dczia/Defcon26-Badge/Images/2018CardFront.jpg

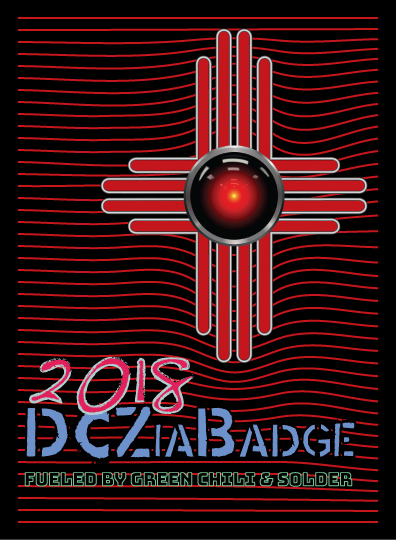
Images/2018CardFront.jpg
