dczia/Defcon26-Badge/Images/DCZia Line Sticker.png

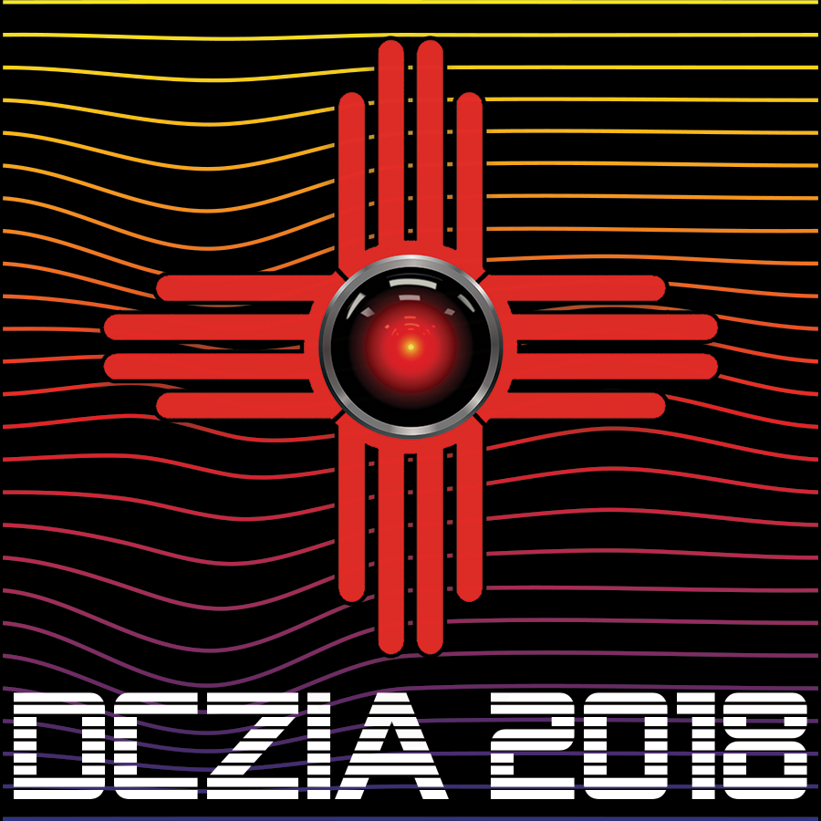
Images/DCZia Line Sticker.png
