dczia/Defcon26-Badge/Images/DCZPolo.png

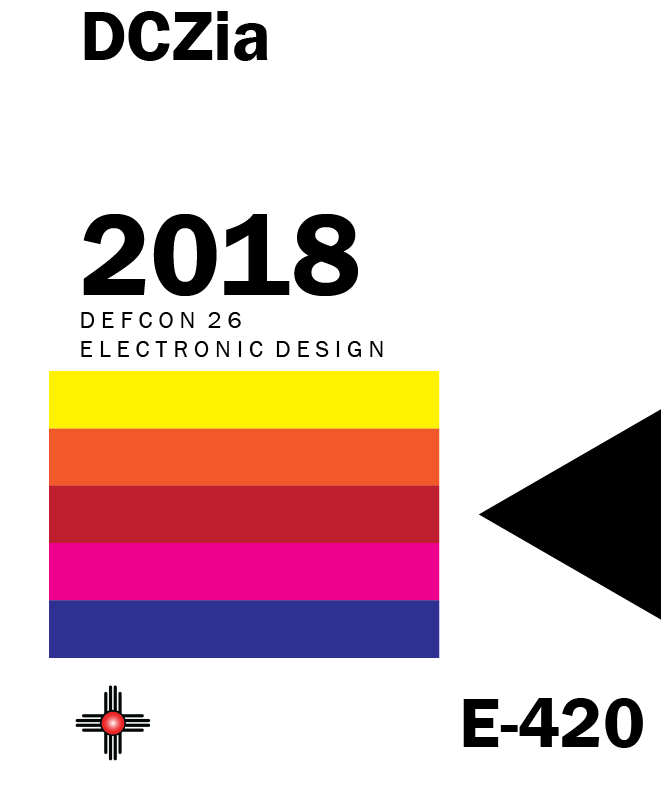
Images/DCZPolo.png
