dczia/Defcon26-Badge/Images/Laynard - FinalArtboard 1@4x.png

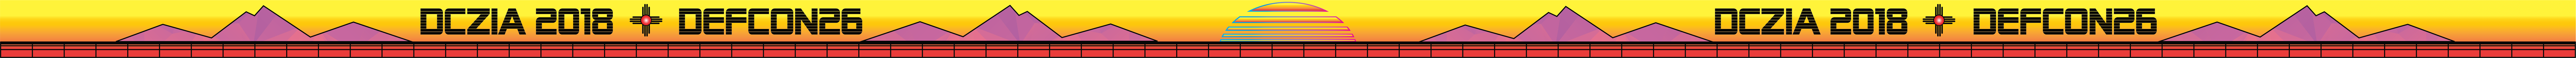
Images/Laynard - FinalArtboard 1@4x.png
