dczia/Defcon26-Badge/Hardware/KeyGridProto/pdf/KeyGridTest1.pdf

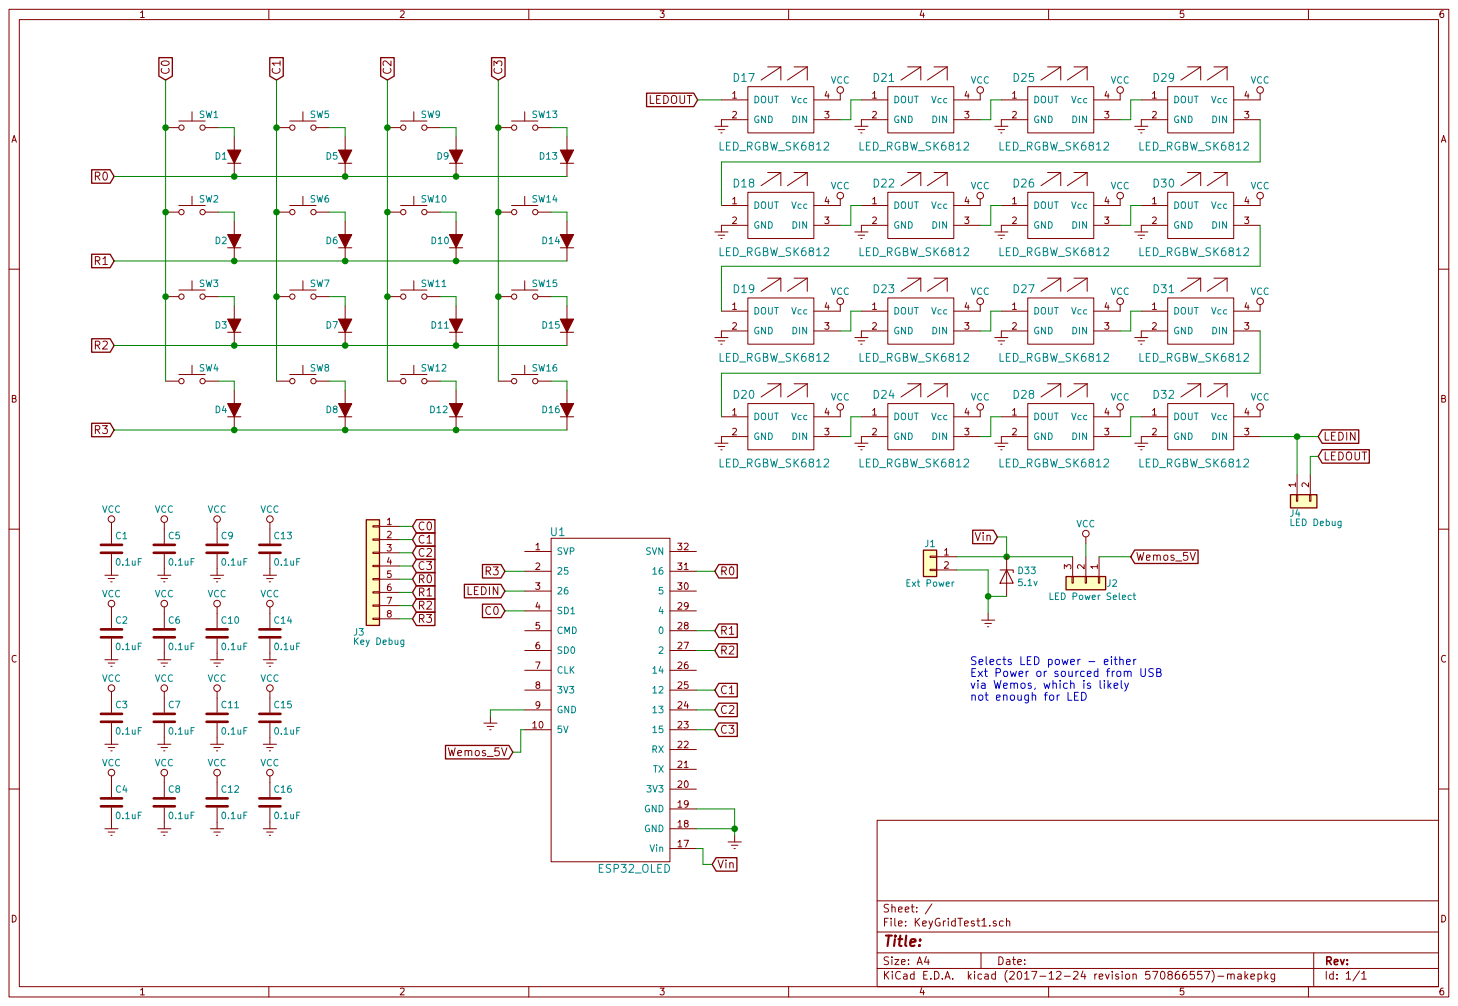
[picture p25: page 1]

Ext Power or sourced from USB
via Wemos, which is likely
not enough for LED
