dczia/Defcon26-Badge/Hardware/KeyGridBadge/gerber/Badge/KeyTest-B.Cu.pdf

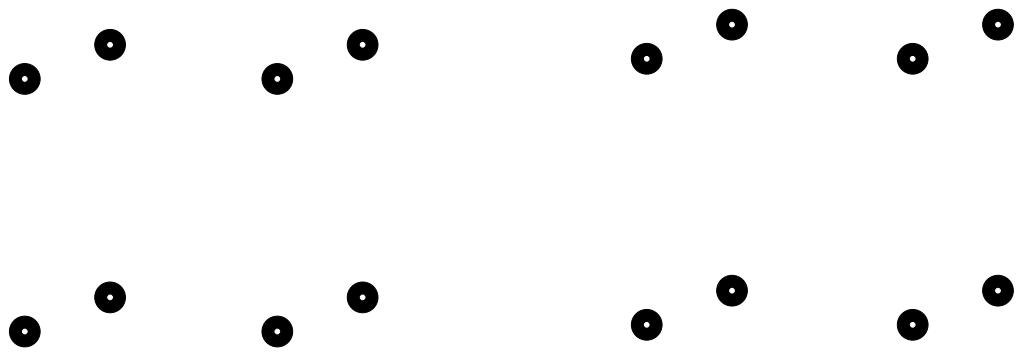
[picture p34: page 1]
