dczia/Defcon26-Badge/Hardware/KeyGridBadge/gerber/Badge/KeyTest-B.Mask.pdf

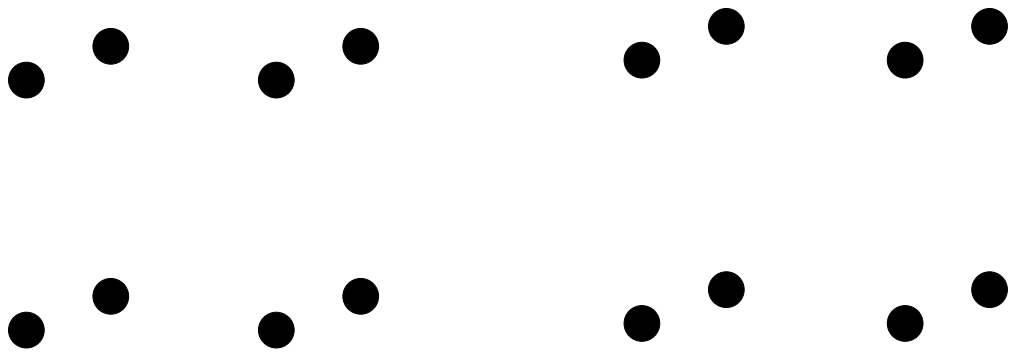
[picture p35: page 1]
