dczia/Defcon26-Badge/Hardware/KeyGridBadge/gerber/Badge/KeyTest-Dwgs.User.pdf

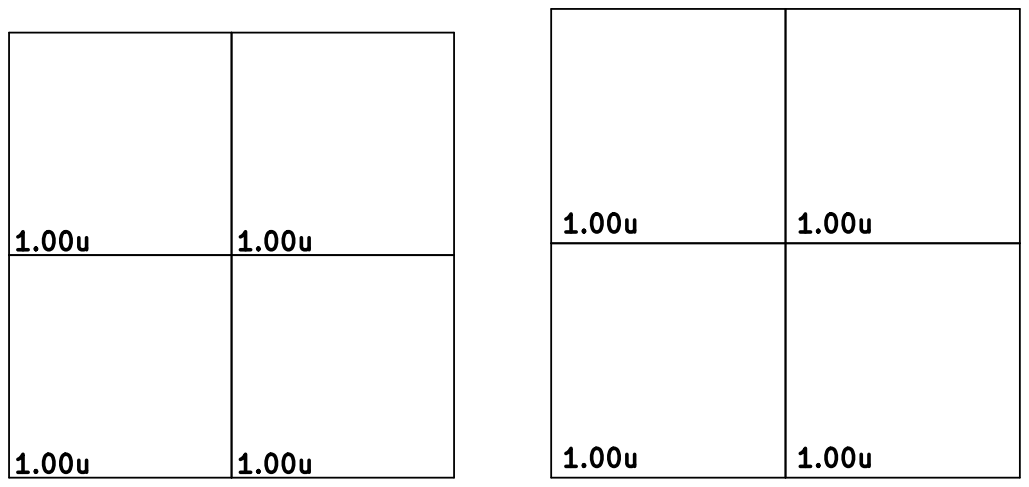
[picture p36: page 1]
