dczia/Defcon26-Badge/Hardware/KeyGridBadge/gerber/Badge/KeyTest-F.SilkS.pdf

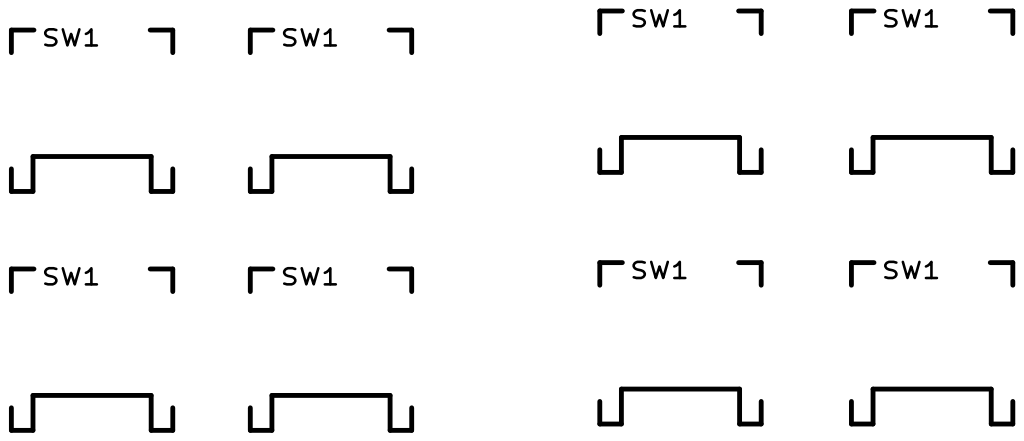
[picture p37: page 1]
