dczia/Defcon26-Badge/Software/dczia26_final/dczia26_keypad.h

#pragma once

/* @file CustomKeypad.pde
|| @version 1.0
|| @author Alexander Brevig
|| @contact alexanderbrevig@gmail.com
||
|| @description
|| | Demonstrates changing the keypad size and key values.
|| #
*/
#include "Keypad.h"

Keypad* keypad_setup(void);


#define KEY_R0C0 '1'
#define KEY_R0C1 '2'
#define KEY_R0C2 '3'
#define KEY_R0C3 'A'
#define KEY_R1C0 '4'
#define KEY_R1C1 '5'
#define KEY_R1C2 '6'
#define KEY_R1C3 'B'
#define KEY_R2C0 '7'
#define KEY_R2C1 '8'
#define KEY_R2C2 '9'
#define KEY_R2C3 'C'
#define KEY_R3C0 '*'
#define KEY_R3C1 '0'
#define KEY_R3C2 '#'
#define KEY_R3C3 'D'

extern Keypad *keys;
