dczia/Defcon26-Badge/Software/dczia26_final/dczia26_oled.h

#pragma once

// For a connection via I2C using Wire include
#include <Wire.h>  // Only needed for Arduino 1.6.5 and earlier
#include <Adafruit_SSD1306.h>

Adafruit_SSD1306* oled_setup(void);

void oled_welcome(Adafruit_SSD1306 *screen);

void oled_drawLines(Adafruit_SSD1306 *screen);
void oled_drawRect(Adafruit_SSD1306 *screen);
void oled_drawZia(Adafruit_SSD1306 *screen);
void oled_fillRect(Adafruit_SSD1306 *screen);
void oled_drawCircle(Adafruit_SSD1306 *screen);
void oled_displaytest(Adafruit_SSD1306 *screen);
void oled_displayCredits(Adafruit_SSD1306 *screen);

const int DISPLAY_WIDTH = 128;
const int DISPLAY_HEIGHT = 32;

const int dczia_size = 32;
const uint8_t zia[] PROGMEM =
{ // 32x32
  0x00, 0x04, 0x20, 0x00,
  0x00, 0x04, 0x20, 0x00,
  0x00, 0x04, 0x20, 0x00,
  0x00, 0x84, 0x21, 0x00,
  0x00, 0x84, 0x21, 0x00,
  0x00, 0x84, 0x21, 0x00,
  0x00, 0x84, 0x21, 0x00,
  0x00, 0x84, 0x21, 0x00,
  0x00, 0x8c, 0x31, 0x00,
  0x00, 0x8f, 0xf1, 0x00,
  0x00, 0x8f, 0xf1, 0x00,
  0x0f, 0xf3, 0xcf, 0xf0,
  0x00, 0xe0, 0x0E, 0x00,
  0x00, 0xe0, 0x0E, 0x00,
  0xff, 0x70, 0x70, 0xff,
  0x00, 0x70, 0x70, 0x00,
  0x00, 0x70, 0x70, 0x00,
  0xff, 0x70, 0x70, 0xff,
  0x00, 0xe0, 0x0E, 0x00,
  0x00, 0xe0, 0x0E, 0x00,
  0x0f, 0xf3, 0xcf, 0xf0,
  0x00, 0x8f, 0xf1, 0x00,
  0x00, 0x8f, 0xf1, 0x00,
  0x00, 0x8c, 0x31, 0x00,
  0x00, 0x84, 0x21, 0x00,
  0x00, 0x84, 0x21, 0x00,
  0x00, 0x84, 0x21, 0x00,
  0x00, 0x84, 0x21, 0x00,
  0x00, 0x04, 0x20, 0x00,
  0x00, 0x04, 0x20, 0x00,
  0x00, 0x04, 0x20, 0x00,
  0x00, 0x04, 0x20, 0x00
};
